ekibanu4/STM_32_Clock/Core/Src/boards/l010f4p6/oled_128x32.c

#include "oled_128x32.h"

#include "stm32l0xx_hal.h"

#define OLED_SCL_GPIO GPIOA
#define OLED_SCL_PIN GPIO_PIN_9
#define OLED_SDA_GPIO GPIOA
#define OLED_SDA_PIN GPIO_PIN_10
#define OLED_ADDR_PRIMARY 0x3CU
#define OLED_ADDR_SECONDARY 0x3DU
#define OLED_WIDTH 128U
#define OLED_PAGE_COUNT 4U
#define OLED_TIME_COLUMN 16U
#define OLED_TIME_PAGE 1U
#define OLED_MODE_COLUMN 16U
#define OLED_MODE_PAGE 1U
#define OLED_EDIT_MARK_PAGE 0U
#define OLED_TIME_MARK_HOUR_COLUMN 22U
#define OLED_TIME_MARK_MINUTE_COLUMN 58U
#define OLED_DATE_MARK_DAY_COLUMN 22U
#define OLED_DATE_MARK_MONTH_COLUMN 58U
#define OLED_DATE_MARK_YEAR_COLUMN 94U
#define OLED_ALARM_LABEL_COLUMN 0U
#define OLED_ALARM_EDIT_COLUMN 10U
#define OLED_ALARM_EDIT_PAGE 1U
#define OLED_ALARM_EDIT_STATUS_COLUMN 108U
#define OLED_ALARM_EDIT_MARK_HOUR_COLUMN 50U
#define OLED_ALARM_EDIT_MARK_MINUTE_COLUMN 86U
#define OLED_ALARM_MAX_ROWS 3U
#define OLED_ALARM_INDICATOR_COLUMN 122U
#define OLED_ALARM_INDICATOR_PAGE 3U
#define OLED_I2C_DELAY_CYCLES 8U
#define OLED_POWER_ON_DELAY_MS 80U
#define OLED_PROBE_RETRIES 3U
#define OLED_TEXT_CHUNK_COLUMNS 24U

static uint8_t oledAddress = OLED_ADDR_PRIMARY;
static uint8_t oledReady = 0U;
static uint8_t oledForceRedraw = 0U;

static void I2cDelay(void) {
  for (volatile uint8_t index = 0U; index < OLED_I2C_DELAY_CYCLES; ++index) {
  }
}

static void SclHigh(void) {
  HAL_GPIO_WritePin(OLED_SCL_GPIO, OLED_SCL_PIN, GPIO_PIN_SET);
  I2cDelay();
}

static void SclLow(void) {
  HAL_GPIO_WritePin(OLED_SCL_GPIO, OLED_SCL_PIN, GPIO_PIN_RESET);
  I2cDelay();
}

static void SdaHigh(void) {
  HAL_GPIO_WritePin(OLED_SDA_GPIO, OLED_SDA_PIN, GPIO_PIN_SET);
  I2cDelay();
}

static void SdaLow(void) {
  HAL_GPIO_WritePin(OLED_SDA_GPIO, OLED_SDA_PIN, GPIO_PIN_RESET);
  I2cDelay();
}

static GPIO_PinState SdaRead(void) {
  return HAL_GPIO_ReadPin(OLED_SDA_GPIO, OLED_SDA_PIN);
}

static void I2cStart(void) {
  SdaHigh();
  SclHigh();
  SdaLow();
  SclLow();
}

static void I2cStop(void) {
  SdaLow();
  SclHigh();
  SdaHigh();
}

static void I2cRecoverBus(void) {
  SdaHigh();
  for (uint8_t pulse = 0U; pulse < 9U; ++pulse) {
    SclHigh();
    SclLow();
  }
  I2cStop();
}

static uint8_t I2cWriteByte(uint8_t value) {
  for (uint8_t bit = 0U; bit < 8U; ++bit) {
    if ((value & 0x80U) != 0U) {
      SdaHigh();
    } else {
      SdaLow();
    }
    SclHigh();
    SclLow();
    value <<= 1;
  }

  SdaHigh();
  SclHigh();
  uint8_t ack = (SdaRead() == GPIO_PIN_RESET) ? 1U : 0U;
  SclLow();
  return ack;
}

static uint8_t Oled_Write(uint8_t address, uint8_t control, const uint8_t *data,
                          uint8_t size) {
  I2cStart();
  if (I2cWriteByte((uint8_t)(address << 1)) == 0U) {
    I2cStop();
    return 0U;
  }
  if (I2cWriteByte(control) == 0U) {
    I2cStop();
    return 0U;
  }
  for (uint8_t index = 0U; index < size; ++index) {
    if (I2cWriteByte(data[index]) == 0U) {
      I2cStop();
      return 0U;
    }
  }
  I2cStop();
  return 1U;
}

static uint8_t Oled_WriteCommand(uint8_t command) {
  return Oled_Write(oledAddress, 0x00U, &command, 1U);
}

static uint8_t Oled_SetCursor(uint8_t page, uint8_t column) {
  if (Oled_WriteCommand((uint8_t)(0xB0U | (page & 0x07U))) == 0U) {
    return 0U;
  }
  if (Oled_WriteCommand((uint8_t)(0x00U | (column & 0x0FU))) == 0U) {
    return 0U;
  }
  return Oled_WriteCommand((uint8_t)(0x10U | ((column >> 4) & 0x0FU)));
}

static uint8_t Oled_GlyphColumn(char symbol, uint8_t column) {
  switch (symbol) {
  case '0': {
    static const uint8_t glyph[5] = {0x3EU, 0x51U, 0x49U, 0x45U, 0x3EU};
    return glyph[column];
  }
  case '1': {
    static const uint8_t glyph[5] = {0x00U, 0x42U, 0x7FU, 0x40U, 0x00U};
    return glyph[column];
  }
  case '2': {
    static const uint8_t glyph[5] = {0x42U, 0x61U, 0x51U, 0x49U, 0x46U};
    return glyph[column];
  }
  case '3': {
    static const uint8_t glyph[5] = {0x21U, 0x41U, 0x45U, 0x4BU, 0x31U};
    return glyph[column];
  }
  case '4': {
    static const uint8_t glyph[5] = {0x18U, 0x14U, 0x12U, 0x7FU, 0x10U};
    return glyph[column];
  }
  case '5': {
    static const uint8_t glyph[5] = {0x27U, 0x45U, 0x45U, 0x45U, 0x39U};
    return glyph[column];
  }
  case '6': {
    static const uint8_t glyph[5] = {0x3CU, 0x4AU, 0x49U, 0x49U, 0x30U};
    return glyph[column];
  }
  case '7': {
    static const uint8_t glyph[5] = {0x01U, 0x71U, 0x09U, 0x05U, 0x03U};
    return glyph[column];
  }
  case '8': {
    static const uint8_t glyph[5] = {0x36U, 0x49U, 0x49U, 0x49U, 0x36U};
    return glyph[column];
  }
  case '9': {
    static const uint8_t glyph[5] = {0x06U, 0x49U, 0x49U, 0x29U, 0x1EU};
    return glyph[column];
  }
  case ':': {
    static const uint8_t glyph[5] = {0x00U, 0x36U, 0x36U, 0x00U, 0x00U};
    return glyph[column];
  }
  case '.': {
    static const uint8_t glyph[5] = {0x00U, 0x60U, 0x60U, 0x00U, 0x00U};
    return glyph[column];
  }
  case '-': {
    static const uint8_t glyph[5] = {0x08U, 0x08U, 0x08U, 0x08U, 0x08U};
    return glyph[column];
  }
  case '*': {
    static const uint8_t glyph[5] = {0x14U, 0x08U, 0x3EU, 0x08U, 0x14U};
    return glyph[column];
  }
  case ' ': {
    return 0x00U;
  }
  case 'A': {
    static const uint8_t glyph[5] = {0x7EU, 0x11U, 0x11U, 0x11U, 0x7EU};
    return glyph[column];
  }
  case 'B': {
    static const uint8_t glyph[5] = {0x7FU, 0x49U, 0x49U, 0x49U, 0x36U};
    return glyph[column];
  }
  case 'F': {
    static const uint8_t glyph[5] = {0x7FU, 0x09U, 0x09U, 0x09U, 0x01U};
    return glyph[column];
  }
  case 'H': {
    static const uint8_t glyph[5] = {0x7FU, 0x08U, 0x08U, 0x08U, 0x7FU};
    return glyph[column];
  }
  case 'L': {
    static const uint8_t glyph[5] = {0x7FU, 0x40U, 0x40U, 0x40U, 0x40U};
    return glyph[column];
  }
  case 'M': {
    static const uint8_t glyph[5] = {0x7FU, 0x02U, 0x04U, 0x02U, 0x7FU};
    return glyph[column];
  }
  case 'N': {
    static const uint8_t glyph[5] = {0x7FU, 0x02U, 0x04U, 0x08U, 0x7FU};
    return glyph[column];
  }
  case 'O': {
    static const uint8_t glyph[5] = {0x3EU, 0x41U, 0x41U, 0x41U, 0x3EU};
    return glyph[column];
  }
  case 'R': {
    static const uint8_t glyph[5] = {0x7FU, 0x09U, 0x19U, 0x29U, 0x46U};
    return glyph[column];
  }
  case 'T': {
    static const uint8_t glyph[5] = {0x01U, 0x01U, 0x7FU, 0x01U, 0x01U};
    return glyph[column];
  }
  case '%': {
    static const uint8_t glyph[5] = {0x23U, 0x13U, 0x08U, 0x64U, 0x62U};
    return glyph[column];
  }
  default:
    return 0x00U;
  }
}

static void Oled_WriteText(const char *text, uint8_t page, uint8_t column) {
  uint8_t data[OLED_TEXT_CHUNK_COLUMNS];
  uint8_t outIndex = 0U;

  if (Oled_SetCursor(page, column) == 0U) {
    return;
  }

  while (*text != '\0') {
    if ((outIndex + 6U) > sizeof(data)) {
      if (Oled_Write(oledAddress, 0x40U, data, outIndex) == 0U) {
        return;
      }
      outIndex = 0U;
    }

    for (uint8_t glyphColumn = 0U; glyphColumn < 5U; ++glyphColumn) {
      data[outIndex] = Oled_GlyphColumn(*text, glyphColumn);
      ++outIndex;
    }
    data[outIndex] = 0x00U;
    ++outIndex;
    ++text;
  }

  if (outIndex != 0U) {
    (void)Oled_Write(oledAddress, 0x40U, data, outIndex);
  }
}

static void Oled_Fill(uint8_t value) {
  uint8_t data[16];

  for (uint8_t index = 0U; index < sizeof(data); ++index) {
    data[index] = value;
  }

  for (uint8_t page = 0U; page < OLED_PAGE_COUNT; ++page) {
    if (Oled_SetCursor(page, 0U) == 0U) {
      return;
    }
    for (uint8_t column = 0U; column < OLED_WIDTH; column += sizeof(data)) {
      if (Oled_Write(oledAddress, 0x40U, data, sizeof(data)) == 0U) {
        return;
      }
    }
  }
}

static void Oled_WriteScaledTextRow(const char *text, uint8_t page,
                                    uint8_t column, uint8_t lowerRow) {
  uint8_t data[OLED_TEXT_CHUNK_COLUMNS];
  uint8_t outIndex = 0U;

  if (Oled_SetCursor(page, column) == 0U) {
    return;
  }

  while (*text != '\0') {
    if ((outIndex + 12U) > sizeof(data)) {
      if (Oled_Write(oledAddress, 0x40U, data, outIndex) == 0U) {
        return;
      }
      outIndex = 0U;
    }

    for (uint8_t glyphColumn = 0U; glyphColumn < 5U; ++glyphColumn) {
      uint8_t source = Oled_GlyphColumn(*text, glyphColumn);
      uint8_t top = 0U;
      uint8_t bottom = 0U;

      for (uint8_t bit = 0U; bit < 7U; ++bit) {
        if ((source & (1U << bit)) != 0U) {
          uint8_t scaledBit = (uint8_t)(bit * 2U);
          if (scaledBit < 8U) {
            top |= (uint8_t)(1U << scaledBit);
          } else {
            bottom |= (uint8_t)(1U << (scaledBit - 8U));
          }
          ++scaledBit;
          if (scaledBit < 8U) {
            top |= (uint8_t)(1U << scaledBit);
          } else {
            bottom |= (uint8_t)(1U << (scaledBit - 8U));
          }
        }
      }

      data[outIndex] = (lowerRow == 0U) ? top : bottom;
      ++outIndex;
      data[outIndex] = (lowerRow == 0U) ? top : bottom;
      ++outIndex;
    }
    data[outIndex] = 0x00U;
    ++outIndex;
    data[outIndex] = 0x00U;
    ++outIndex;
    ++text;
  }

  if (outIndex != 0U) {
    (void)Oled_Write(oledAddress, 0x40U, data, outIndex);
  }
}

static void Oled_WriteScaledText(const char *text, uint8_t page,
                                 uint8_t column) {
  Oled_WriteScaledTextRow(text, page, column, 0U);
  Oled_WriteScaledTextRow(text, (uint8_t)(page + 1U), column, 1U);
}

static void Oled_ShowTime(const ClockDateTime_t *dateTime,
                          EditTarget_t editTarget,
                          uint8_t alarmAnyEnabled) {
  char text[9];

  text[0] = (char)('0' + ((dateTime->hours / 10U) % 10U));
  text[1] = (char)('0' + (dateTime->hours % 10U));
  text[2] = ':';
  text[3] = (char)('0' + ((dateTime->minutes / 10U) % 10U));
  text[4] = (char)('0' + (dateTime->minutes % 10U));
  text[5] = ':';
  text[6] = (char)('0' + ((dateTime->seconds / 10U) % 10U));
  text[7] = (char)('0' + (dateTime->seconds % 10U));
  text[8] = '\0';

  Oled_WriteText((editTarget == EDIT_HOURS) ? ".." : "  ", OLED_EDIT_MARK_PAGE,
                 OLED_TIME_MARK_HOUR_COLUMN);
  Oled_WriteText((editTarget == EDIT_MINUTES) ? ".." : "  ",
                 OLED_EDIT_MARK_PAGE, OLED_TIME_MARK_MINUTE_COLUMN);
  Oled_WriteScaledText(text, OLED_TIME_PAGE, OLED_TIME_COLUMN);
  Oled_WriteText((alarmAnyEnabled != 0U) ? "A" : " ", OLED_ALARM_INDICATOR_PAGE,
                 OLED_ALARM_INDICATOR_COLUMN);
}

static void Oled_ShowDate(const ClockDateTime_t *dateTime,
                          EditTarget_t editTarget) {
  char text[9];

  text[0] = (char)('0' + ((dateTime->day / 10U) % 10U));
  text[1] = (char)('0' + (dateTime->day % 10U));
  text[2] = '.';
  text[3] = (char)('0' + ((dateTime->month / 10U) % 10U));
  text[4] = (char)('0' + (dateTime->month % 10U));
  text[5] = '.';
  text[6] = (char)('0' + ((dateTime->year / 10U) % 10U));
  text[7] = (char)('0' + (dateTime->year % 10U));
  text[8] = '\0';

  Oled_WriteText((editTarget == EDIT_DAY) ? ".." : "  ", OLED_EDIT_MARK_PAGE,
                 OLED_DATE_MARK_DAY_COLUMN);
  Oled_WriteText((editTarget == EDIT_MONTH) ? ".." : "  ", OLED_EDIT_MARK_PAGE,
                 OLED_DATE_MARK_MONTH_COLUMN);
  Oled_WriteText((editTarget == EDIT_YEAR) ? ".." : "  ", OLED_EDIT_MARK_PAGE,
                 OLED_DATE_MARK_YEAR_COLUMN);
  Oled_WriteScaledText(text, OLED_MODE_PAGE, OLED_MODE_COLUMN);
}

static void Oled_ShowEnvironment(const ClockEnvironment_t *environment) {
  char text[9] = {'T', '-', '-', ' ', 'H', '-', '-', ' ', '\0'};

  if (environment->isValid != 0U) {
    text[1] = (char)('0' + ((environment->temperature / 10U) % 10U));
    text[2] = (char)('0' + (environment->temperature % 10U));
    text[5] = (char)('0' + ((environment->humidity / 10U) % 10U));
    text[6] = (char)('0' + (environment->humidity % 10U));
  }

  Oled_WriteScaledText(text, OLED_MODE_PAGE, OLED_MODE_COLUMN);
}

static void Oled_ShowBattery(uint16_t batteryPercentTenths) {
  char text[11] = {'B', 'A', 'T', ' ', '0', '0', '.', '0', '%', '\0', '\0'};
  uint8_t wholePercent = (uint8_t)(batteryPercentTenths / 10U);
  uint8_t filledColumns =
      (uint8_t)(((uint32_t)batteryPercentTenths * 120U) / 1000U);
  uint8_t data[16];

  if (wholePercent >= 100U) {
    text[4] = '1';
    text[5] = '0';
    text[6] = '0';
    text[7] = '.';
    text[8] = '0';
    text[9] = '%';
    text[10] = '\0';
  } else {
    text[4] = (char)('0' + ((wholePercent / 10U) % 10U));
    text[5] = (char)('0' + (wholePercent % 10U));
    text[7] = (char)('0' + (batteryPercentTenths % 10U));
  }

  Oled_WriteScaledText(text, OLED_MODE_PAGE, 4U);

  for (uint8_t column = 0U; column < sizeof(data); ++column) {
    data[column] = 0x81U;
  }
  if (Oled_SetCursor(3U, 4U) == 0U) {
    return;
  }
  for (uint8_t column = 0U; column < 120U; column += sizeof(data)) {
    for (uint8_t index = 0U; index < sizeof(data); ++index) {
      uint8_t absoluteColumn = (uint8_t)(column + index);

      if (absoluteColumn >= 120U) {
        data[index] = 0x00U;
      } else if (absoluteColumn < filledColumns) {
        data[index] = 0xFFU;
      } else {
        data[index] = 0x81U;
      }
    }
    if (Oled_Write(oledAddress, 0x40U, data, sizeof(data)) == 0U) {
      return;
    }
  }
}

static uint8_t Oled_IsAlarmEdit(EditTarget_t editTarget) {
  return ((editTarget == EDIT_ALARM_HOURS) ||
          (editTarget == EDIT_ALARM_MINUTES))
             ? 1U
             : 0U;
}

static void Oled_FormatAlarmTime(const AlarmSlot_t *slot, uint8_t slotIndex,
                                 char *text) {
  text[0] = 'A';
  text[1] = (char)('1' + slotIndex);
  text[2] = ' ';
  if ((slot != 0) && (slot->configured != 0U)) {
    text[3] = (char)('0' + ((slot->hour / 10U) % 10U));
    text[4] = (char)('0' + (slot->hour % 10U));
    text[5] = ':';
    text[6] = (char)('0' + ((slot->minute / 10U) % 10U));
    text[7] = (char)('0' + (slot->minute % 10U));
  } else {
    text[3] = '-';
    text[4] = '-';
    text[5] = ':';
    text[6] = '-';
    text[7] = '-';
  }
  text[8] = '\0';
}

static void Oled_FormatAlarmStatus(const AlarmSlot_t *slot, char *text) {
  if ((slot != 0) && (slot->enabled != 0U)) {
    text[0] = 'O';
    text[1] = 'N';
    text[2] = ' ';
  } else {
    text[0] = 'O';
    text[1] = 'F';
    text[2] = 'F';
  }
  text[3] = '\0';
}

static void Oled_ShowAlarmSlot(const AlarmSlot_t *slot, uint8_t slotIndex,
                               uint8_t selected) {
  char text[14];

  text[0] = (selected != 0U) ? '*' : '-';
  Oled_FormatAlarmTime(slot, slotIndex, &text[1]);
  text[9] = ' ';
  Oled_FormatAlarmStatus(slot, &text[10]);

  Oled_WriteText(text, slotIndex, OLED_ALARM_LABEL_COLUMN);
}

static void Oled_ShowAlarmEdit(const AlarmSlot_t *alarmSlots,
                               uint8_t alarmSlotCount,
                               uint8_t selectedAlarmSlot,
                               EditTarget_t editTarget) {
  char timeText[9];
  char statusText[4];

  if ((selectedAlarmSlot >= alarmSlotCount) ||
      (selectedAlarmSlot >= OLED_ALARM_MAX_ROWS)) {
    return;
  }

  if (editTarget == EDIT_ALARM_HOURS) {
    Oled_WriteText("..", 0U, OLED_ALARM_EDIT_MARK_HOUR_COLUMN);
    Oled_WriteText("  ", 0U, OLED_ALARM_EDIT_MARK_MINUTE_COLUMN);
  } else {
    Oled_WriteText("  ", 0U, OLED_ALARM_EDIT_MARK_HOUR_COLUMN);
    Oled_WriteText("..", 0U, OLED_ALARM_EDIT_MARK_MINUTE_COLUMN);
  }

  Oled_FormatAlarmTime(&alarmSlots[selectedAlarmSlot], selectedAlarmSlot,
                       timeText);
  Oled_FormatAlarmStatus(&alarmSlots[selectedAlarmSlot], statusText);
  Oled_WriteScaledText(timeText, OLED_ALARM_EDIT_PAGE, OLED_ALARM_EDIT_COLUMN);
  Oled_WriteText(statusText, 3U, OLED_ALARM_EDIT_STATUS_COLUMN);
}

static void Oled_ShowAlarm(const AlarmSlot_t *alarmSlots, uint8_t alarmSlotCount,
                           uint8_t selectedAlarmSlot, EditTarget_t editTarget) {
  uint8_t rows = alarmSlotCount;

  if (Oled_IsAlarmEdit(editTarget) != 0U) {
    Oled_ShowAlarmEdit(alarmSlots, alarmSlotCount, selectedAlarmSlot,
                       editTarget);
    return;
  }

  if (rows > OLED_ALARM_MAX_ROWS) {
    rows = OLED_ALARM_MAX_ROWS;
  }

  for (uint8_t index = 0U; index < rows; ++index) {
    Oled_ShowAlarmSlot(&alarmSlots[index], index,
                       (index == selectedAlarmSlot) ? 1U : 0U);
  }
}

static uint8_t Oled_Probe(uint8_t address) {
  I2cStart();
  uint8_t ack = I2cWriteByte((uint8_t)(address << 1));
  I2cStop();
  return ack;
}

static void Oled_GpioInit(void) {
  GPIO_InitTypeDef GPIO_InitStruct = {0};

  __HAL_RCC_GPIOA_CLK_ENABLE();

  GPIO_InitStruct.Pin = OLED_SCL_PIN | OLED_SDA_PIN;
  GPIO_InitStruct.Mode = GPIO_MODE_OUTPUT_OD;
  GPIO_InitStruct.Pull = GPIO_PULLUP;
  GPIO_InitStruct.Speed = GPIO_SPEED_FREQ_LOW;
  HAL_GPIO_Init(GPIOA, &GPIO_InitStruct);

  HAL_GPIO_WritePin(GPIOA, OLED_SCL_PIN | OLED_SDA_PIN, GPIO_PIN_SET);
}

void Oled128x32_Init(void) {
  static const uint8_t initCommands[] = {
      0xAEU, 0x20U, 0x00U, 0x40U, 0xA1U, 0xC8U, 0x81U, 0x7FU,
      0xA6U, 0xA8U, 0x1FU, 0xD3U, 0x00U, 0xD5U, 0x80U, 0xD9U,
      0xF1U, 0xDAU, 0x02U, 0xDBU, 0x40U, 0x8DU, 0x14U, 0xAFU};

  Oled_GpioInit();
  HAL_Delay(OLED_POWER_ON_DELAY_MS);
  I2cRecoverBus();

  for (uint8_t attempt = 0U; attempt < OLED_PROBE_RETRIES; ++attempt) {
    oledAddress = OLED_ADDR_PRIMARY;
    if (Oled_Probe(oledAddress) != 0U) {
      break;
    }
    oledAddress = OLED_ADDR_SECONDARY;
    if (Oled_Probe(oledAddress) != 0U) {
      break;
    }
    if ((attempt + 1U) >= OLED_PROBE_RETRIES) {
      oledReady = 0U;
      return;
    }
    HAL_Delay(20U);
    I2cRecoverBus();
  }

  for (uint8_t index = 0U; index < sizeof(initCommands); ++index) {
    if (Oled_WriteCommand(initCommands[index]) == 0U) {
      oledReady = 0U;
      return;
    }
  }

  oledReady = 1U;
  Oled_Fill(0x00U);
}

void Oled128x32_Clear(void) {
  if (oledReady != 0U) {
    Oled_Fill(0x00U);
  }
}

void Oled128x32_ShowAlarm(uint8_t alarmSlot) {
  char text[8] = {'A', 'L', 'A', 'R', 'M', ' ', '?', '\0'};

  if (oledReady == 0U) {
    return;
  }

  if (alarmSlot < OLED_ALARM_MAX_ROWS) {
    text[6] = (char)('1' + alarmSlot);
  }

  Oled_Fill(0x00U);
  Oled_WriteScaledText(text, 1U, 22U);
  oledForceRedraw = 1U;
}

void Oled128x32_Render(uint32_t nowMs, DisplayMode_t displayMode,
                     const ClockDateTime_t *dateTime,
                     const ClockEnvironment_t *environment,
                     const AlarmSlot_t *alarmSlots, uint8_t alarmSlotCount,
                     uint8_t selectedAlarmSlot, EditTarget_t editTarget,
                     uint16_t batteryPercentTenths,
                     uint8_t alarmAnyEnabled) {
  static uint32_t lastDrawMs = 0xFFFFFFFFUL;
  static DisplayMode_t lastDisplayMode = DISPLAY_ALARM;
  static uint8_t lastHour = 0xFFU;
  static uint8_t lastMinute = 0xFFU;
  static uint8_t lastSecond = 0xFFU;
  static uint8_t lastDay = 0xFFU;
  static uint8_t lastMonth = 0xFFU;
  static uint8_t lastYear = 0xFFU;
  static uint8_t lastTemperature = 0xFFU;
  static uint8_t lastHumidity = 0xFFU;
  static uint8_t lastEnvironmentValid = 0xFFU;
  static uint8_t lastSelectedAlarmSlot = 0xFFU;
  static uint8_t lastAlarmAnyEnabled = 0xFFU;
  static uint16_t lastBatteryPercentTenths = 0xFFFFU;
  static EditTarget_t lastEditTarget = EDIT_NONE;
  static AlarmSlot_t lastAlarmSlots[OLED_ALARM_MAX_ROWS];
  uint8_t shouldDraw = 0U;
  uint8_t modeChanged = 0U;
  DisplayMode_t previousDisplayMode = lastDisplayMode;
  EditTarget_t previousEditTarget = lastEditTarget;
  uint8_t alarmEditStateChanged = 0U;

  if (oledReady == 0U) {
    return;
  }

  if (oledForceRedraw != 0U) {
    shouldDraw = 1U;
    modeChanged = 1U;
    oledForceRedraw = 0U;
  } else if (displayMode != lastDisplayMode) {
    shouldDraw = 1U;
    modeChanged = 1U;
  } else if (displayMode == DISPLAY_TIME) {
    shouldDraw = ((dateTime->hours != lastHour) ||
                  (dateTime->minutes != lastMinute) ||
                  (dateTime->seconds != lastSecond) ||
                  (editTarget != lastEditTarget) ||
                  (alarmAnyEnabled != lastAlarmAnyEnabled))
                     ? 1U
                     : 0U;
  } else if (displayMode == DISPLAY_DATE) {
    shouldDraw = ((dateTime->day != lastDay) || (dateTime->month != lastMonth) ||
                  (dateTime->year != lastYear) ||
                  (editTarget != lastEditTarget))
                     ? 1U
                     : 0U;
  } else if (displayMode == DISPLAY_ENVIRONMENT) {
    shouldDraw = ((environment->isValid != lastEnvironmentValid) ||
                  (environment->temperature != lastTemperature) ||
                  (environment->humidity != lastHumidity))
                     ? 1U
                     : 0U;
  } else if (displayMode == DISPLAY_ALARM) {
    uint8_t rows = alarmSlotCount;

    if (rows > OLED_ALARM_MAX_ROWS) {
      rows = OLED_ALARM_MAX_ROWS;
    }

    shouldDraw =
        ((selectedAlarmSlot != lastSelectedAlarmSlot) ||
         (editTarget != lastEditTarget))
            ? 1U
            : 0U;
    for (uint8_t index = 0U; index < rows; ++index) {
      if ((alarmSlots[index].configured != lastAlarmSlots[index].configured) ||
          (alarmSlots[index].enabled != lastAlarmSlots[index].enabled) ||
          (alarmSlots[index].hour != lastAlarmSlots[index].hour) ||
          (alarmSlots[index].minute != lastAlarmSlots[index].minute)) {
        shouldDraw = 1U;
      }
    }
  } else if (displayMode == DISPLAY_BATTERY) {
    shouldDraw = (batteryPercentTenths != lastBatteryPercentTenths) ? 1U : 0U;
  }

  if (shouldDraw == 0U) {
    return;
  }

  if ((lastDrawMs != 0xFFFFFFFFUL) && ((nowMs - lastDrawMs) < 200U)) {
    return;
  }

  lastDrawMs = nowMs;
  lastDisplayMode = displayMode;
  lastHour = dateTime->hours;
  lastMinute = dateTime->minutes;
  lastSecond = dateTime->seconds;
  lastDay = dateTime->day;
  lastMonth = dateTime->month;
  lastYear = dateTime->year;
  lastTemperature = environment->temperature;
  lastHumidity = environment->humidity;
  lastEnvironmentValid = environment->isValid;
  lastSelectedAlarmSlot = selectedAlarmSlot;
  lastAlarmAnyEnabled = alarmAnyEnabled;
  lastBatteryPercentTenths = batteryPercentTenths;
  lastEditTarget = editTarget;
  {
    uint8_t rows = alarmSlotCount;

    if (rows > OLED_ALARM_MAX_ROWS) {
      rows = OLED_ALARM_MAX_ROWS;
    }
    for (uint8_t index = 0U; index < rows; ++index) {
      lastAlarmSlots[index] = alarmSlots[index];
    }
  }

  alarmEditStateChanged =
      ((displayMode == DISPLAY_ALARM) &&
       (Oled_IsAlarmEdit(editTarget) != Oled_IsAlarmEdit(previousEditTarget)))
          ? 1U
          : 0U;

  if ((modeChanged != 0U) || (alarmEditStateChanged != 0U)) {
    if ((displayMode == DISPLAY_ALARM) ||
        (displayMode == DISPLAY_BATTERY) ||
        (previousDisplayMode == DISPLAY_ALARM) ||
        (previousDisplayMode == DISPLAY_BATTERY) ||
        (Oled_IsAlarmEdit(editTarget) != Oled_IsAlarmEdit(previousEditTarget))) {
      Oled_Fill(0x00U);
    }
  }

  if (displayMode == DISPLAY_DATE) {
    Oled_ShowDate(dateTime, editTarget);
  } else if (displayMode == DISPLAY_ENVIRONMENT) {
    Oled_ShowEnvironment(environment);
  } else if (displayMode == DISPLAY_ALARM) {
    Oled_ShowAlarm(alarmSlots, alarmSlotCount, selectedAlarmSlot, editTarget);
  } else if (displayMode == DISPLAY_BATTERY) {
    Oled_ShowBattery(batteryPercentTenths);
  } else {
    Oled_ShowTime(dateTime, editTarget, alarmAnyEnabled);
  }
}
